projetsdiy/anemometre-connect-esp8266/Cura/anémomètre - blocage esp8266.png

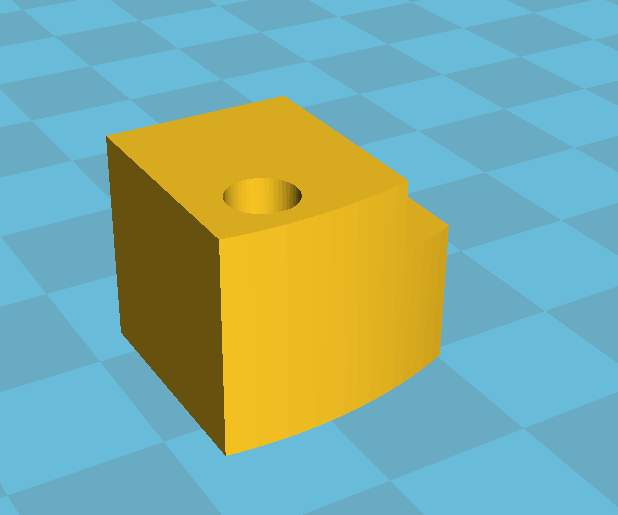
Cura/anémomètre - blocage esp8266.png
