projetsdiy/anemometre-connect-esp8266/Cura/Anémomètre - capot supérieur.png

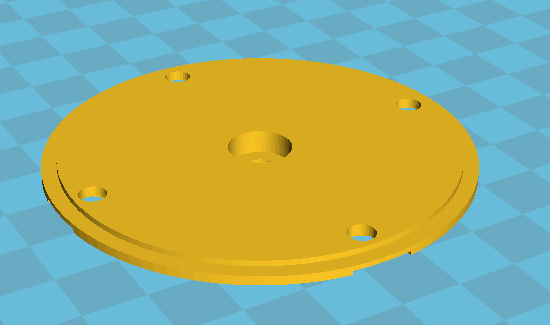
Cura/Anémomètre - capot supérieur.png
