projetsdiy/anemometre-connect-esp8266/Cura/Girouette - boitier - disque encodeur - support leds.png

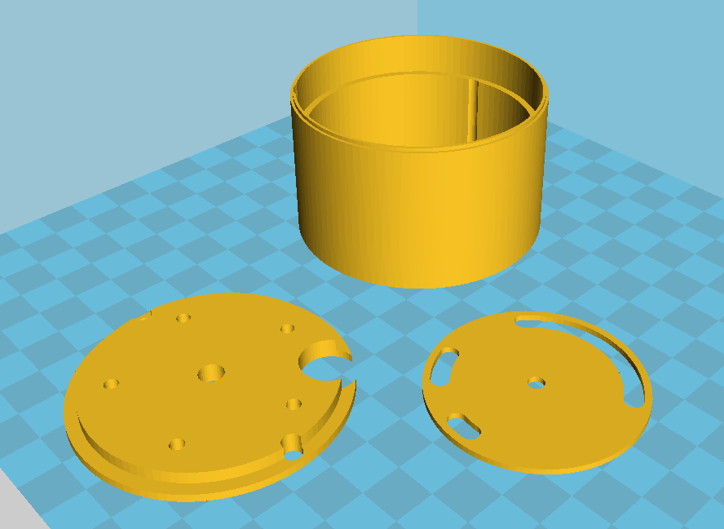
Cura/Girouette - boitier - disque encodeur - support leds.png
