projetsdiy/anemometre-connect-esp8266/Cura/Plaque de liaison - axe central.png

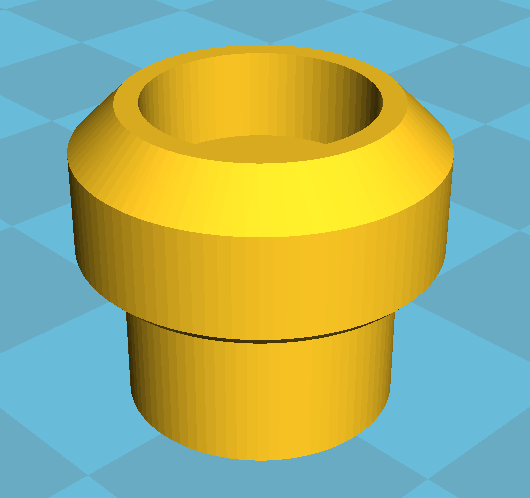
Cura/Plaque de liaison - axe central.png
