projetsdiy/anemometre-connect-esp8266/STL/Anemometre - support us1881.stl

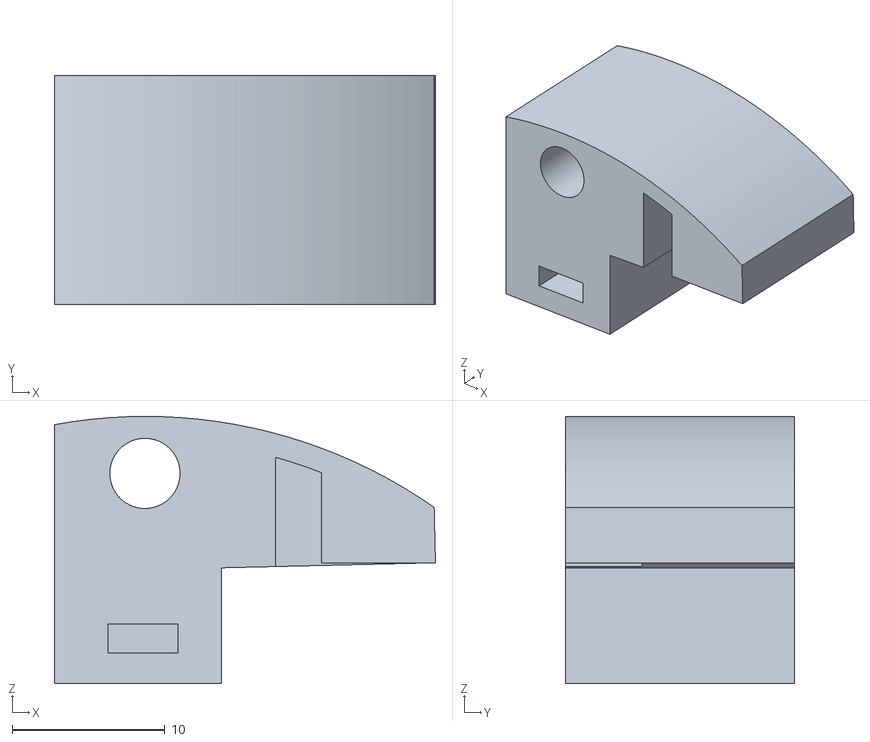
[picture p25: CAD file, 2016-06-16]
STL/Anemometre - support us1881.stl
25.0 x 15.0 x 17.5
