projetsdiy/anemometre-connect-esp8266/STL/Girouette - boitier.stl

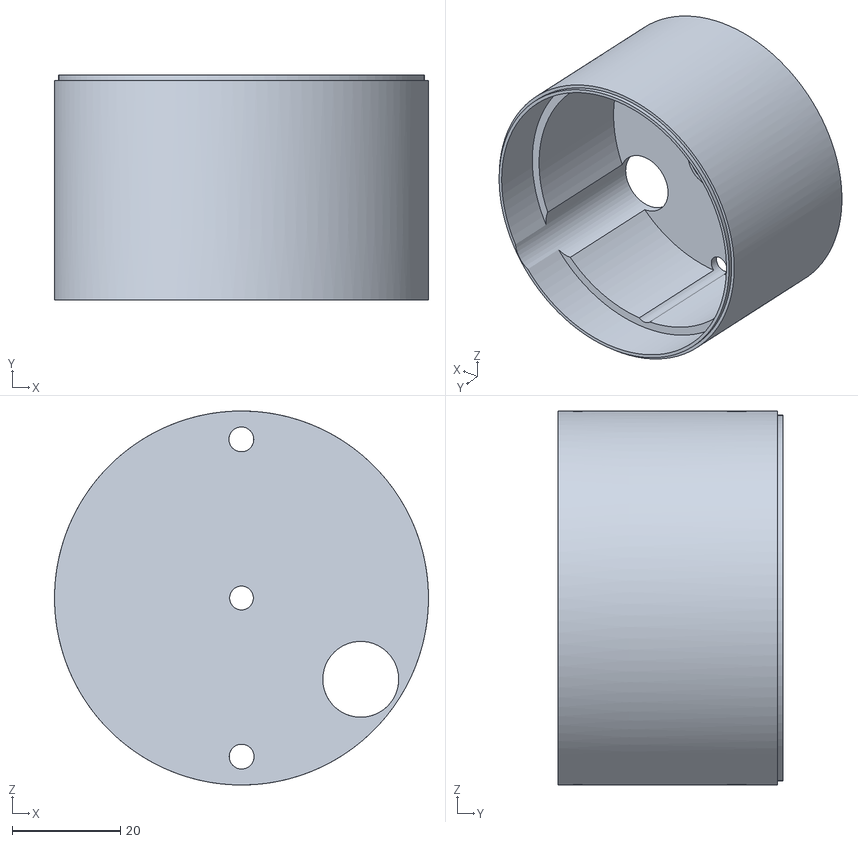
[picture p26: CAD file, 2016-06-16]
STL/Girouette - boitier.stl
69.0 x 41.5 x 69.0
